EricLarueMartin/MMCX_2DD-100P/MMCX_2DD-100P_Even.png

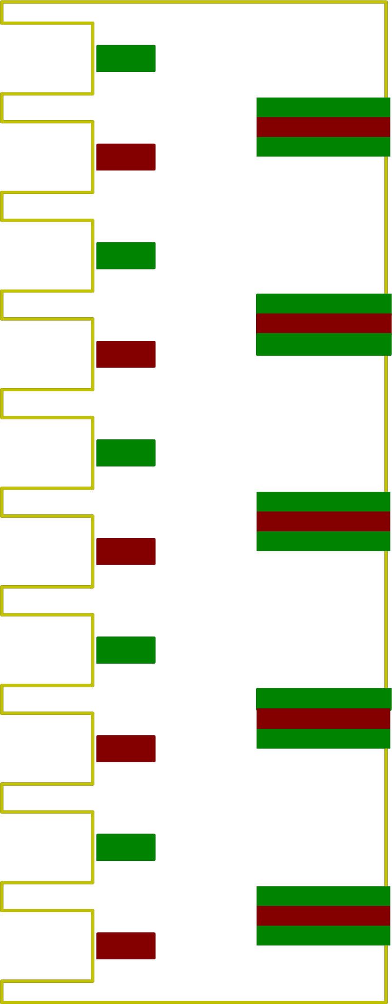
MMCX_2DD-100P_Even.png
