EricLarueMartin/MMCX_2DD-100P/c-1-1757819-0-k-3d.stp

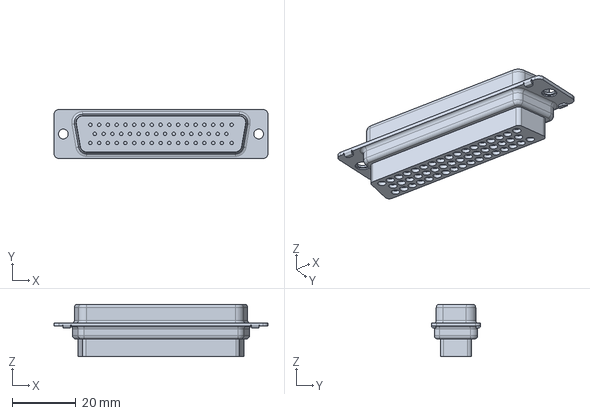
[picture p15: CAD file, 2021-01-05]
c-1-1757819-0-k-3d.stp
66.9 x 15.4 x 16.4 mm
